interspecifics/ComunicacionesEspeculativas/Impresion 3d XY/XY/Eje X 2.stl

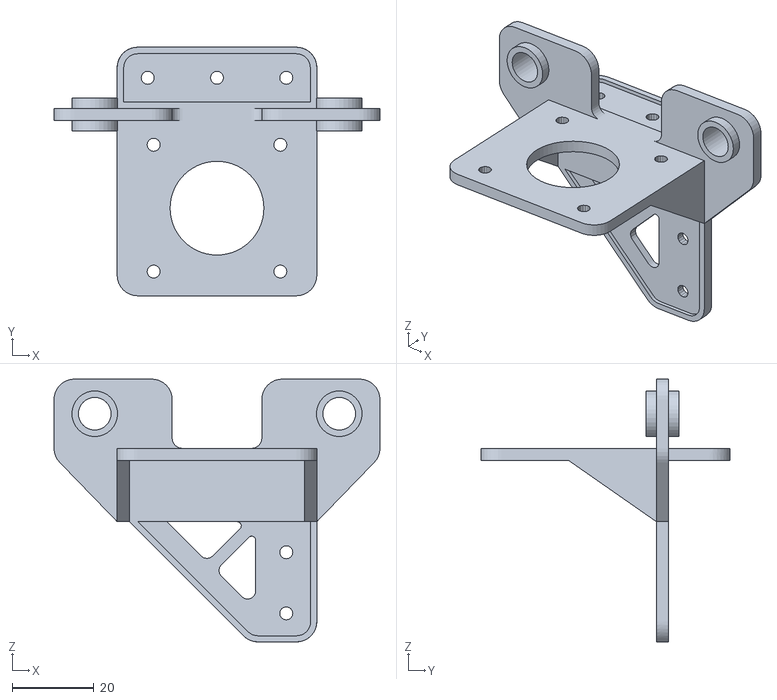
[picture p22: CAD file, 2019-01-10]
Impresion 3d XY/XY/Eje X 2.stl
80.0 x 61.0 x 64.5
