interspecifics/ComunicacionesEspeculativas/3D_files/CE_optics/CE_RPIcam_cover.stl

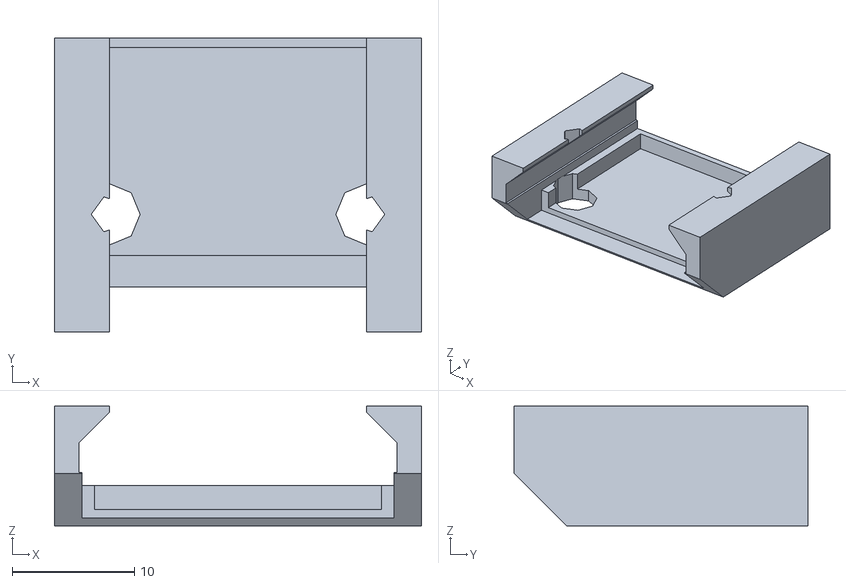
[picture p23: CAD file, 2018-02-25]
3D_files/CE_optics/CE_RPIcam_cover.stl
30.0 x 24.0 x 9.80
