interspecifics/ComunicacionesEspeculativas/Impresion 3d XY/OpenBeam/L Bracket.STL

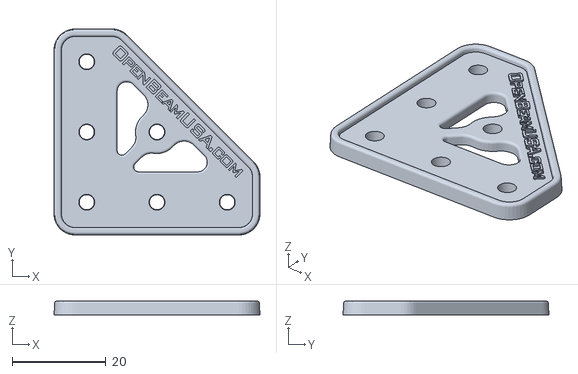
[picture p24: CAD file, 2019-01-10]
Impresion 3d XY/OpenBeam/L Bracket.STL
44.0 x 44.0 x 3.00
