interspecifics/ComunicacionesEspeculativas/Impresion 3d XY/Stage/Bearing Mount Right Bottom.STL

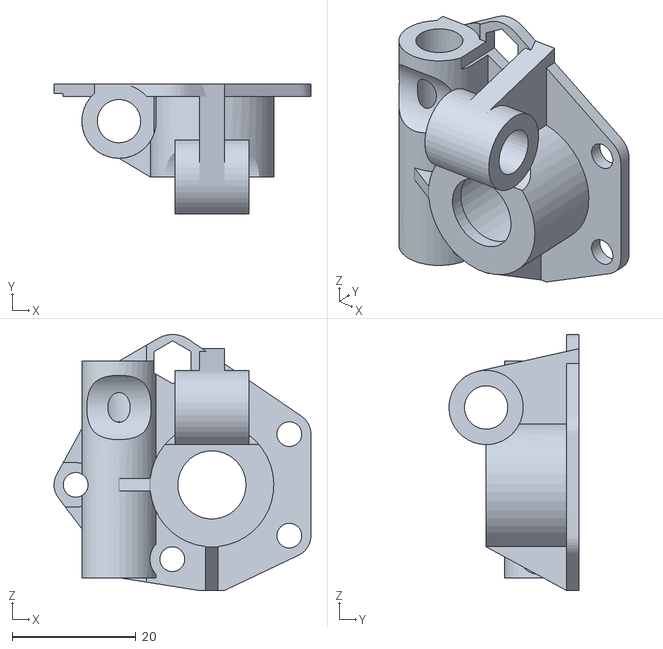
[picture p25: CAD file, 2019-01-10]
Impresion 3d XY/Stage/Bearing Mount Right Bottom.STL
41.5 x 21.0 x 41.4
