interspecifics/ComunicacionesEspeculativas/Impresion 3d XY/XY/Eje Y trasero.stl

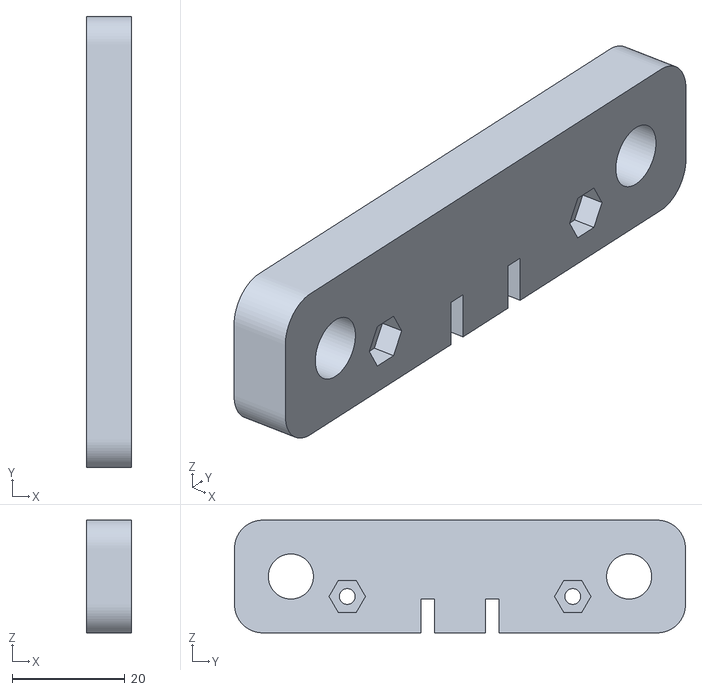
[picture p26: CAD file, 2019-01-10]
Impresion 3d XY/XY/Eje Y trasero.stl
8.00 x 80.0 x 20.0
