interspecifics/ComunicacionesEspeculativas/Impresion 3d XY/OpenBeam/T Bracket.STL

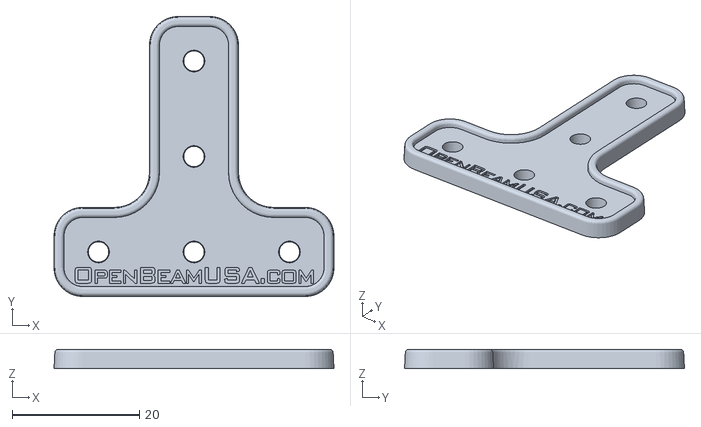
[picture p27: CAD file, 2019-01-10]
Impresion 3d XY/OpenBeam/T Bracket.STL
44.0 x 44.0 x 3.00
