interspecifics/ComunicacionesEspeculativas/Impresion 3d XY/XY/Eje Y Tensor.stl

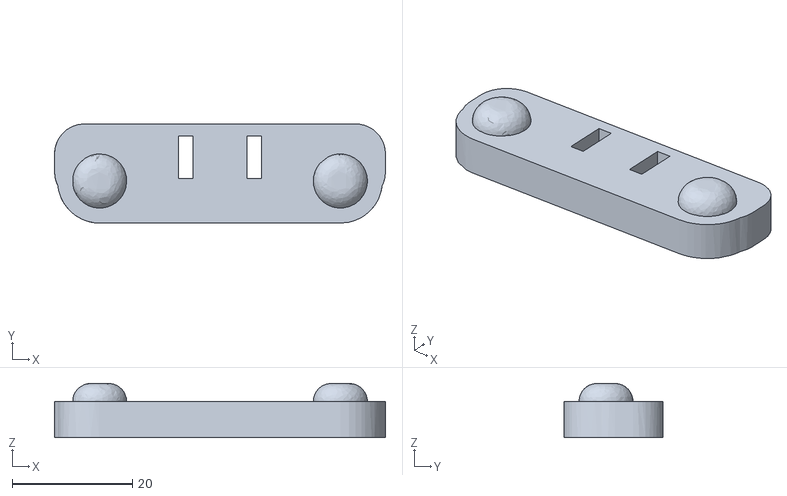
[picture p28: CAD file, 2019-01-10]
Impresion 3d XY/XY/Eje Y Tensor.stl
55.0 x 16.5 x 9.00
