interspecifics/ComunicacionesEspeculativas/Impresion 3d XY/Stage/Front stage Mount.stl

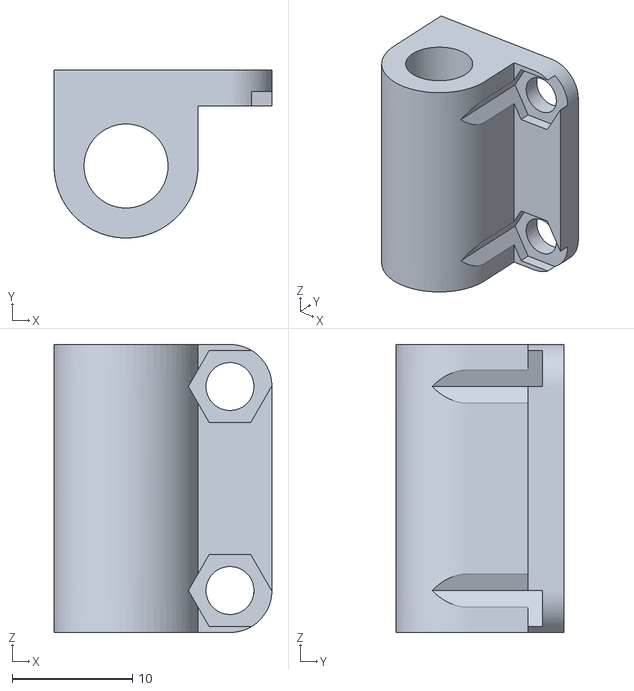
[picture p29: CAD file, 2019-01-10]
Impresion 3d XY/Stage/Front stage Mount.stl
18.2 x 14.0 x 24.0
